transistorfet/computie/docs/posts/images/2021-09-Z80-breadboard-with-memory.jpg

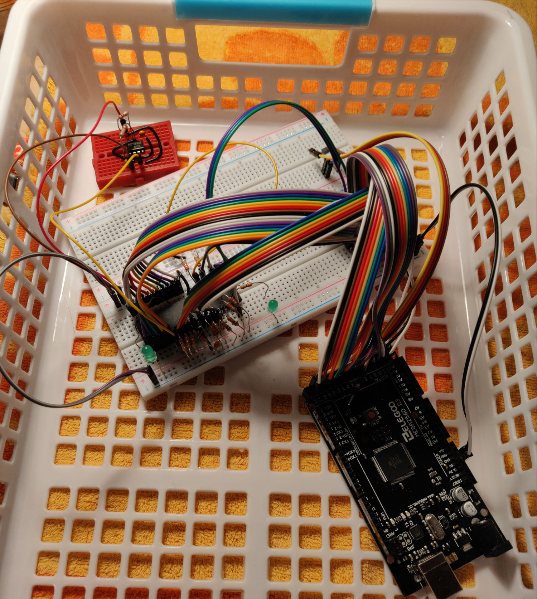
docs/posts/images/2021-09-Z80-breadboard-with-memory.jpg
