transistorfet/computie/docs/posts/images/2021-09-Z80-full-system.jpg

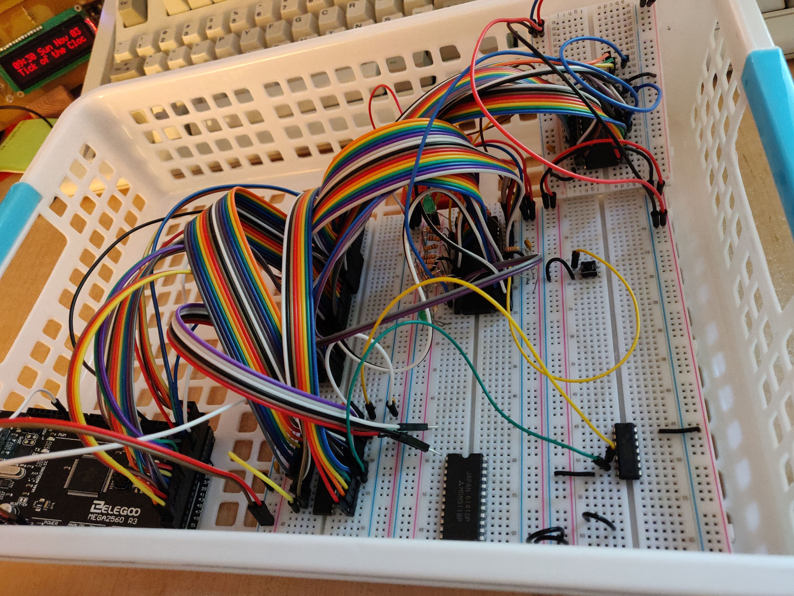
docs/posts/images/2021-09-Z80-full-system.jpg
