transistorfet/computie/images/68k-SBC-rev2/SBC-full.jpg

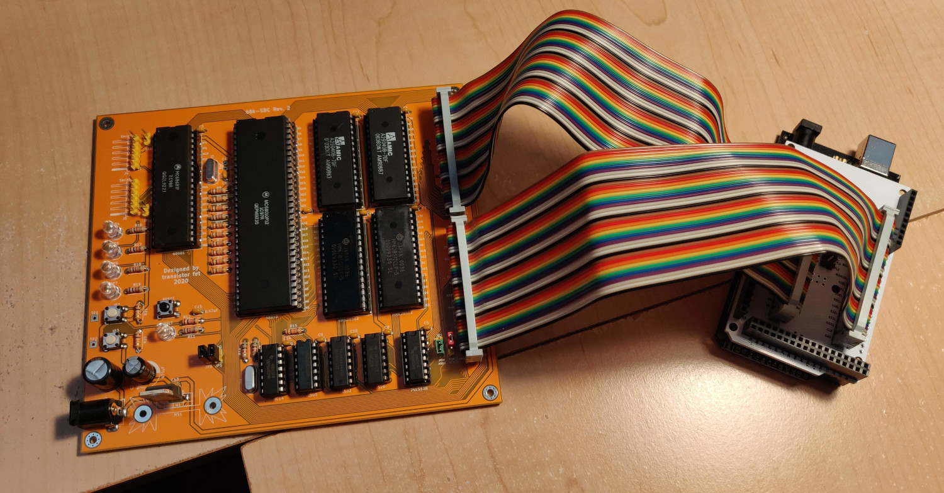
images/68k-SBC-rev2/SBC-full.jpg
