transistorfet/computie/images/68k-SMT-rev1/PCB-bottom.jpg

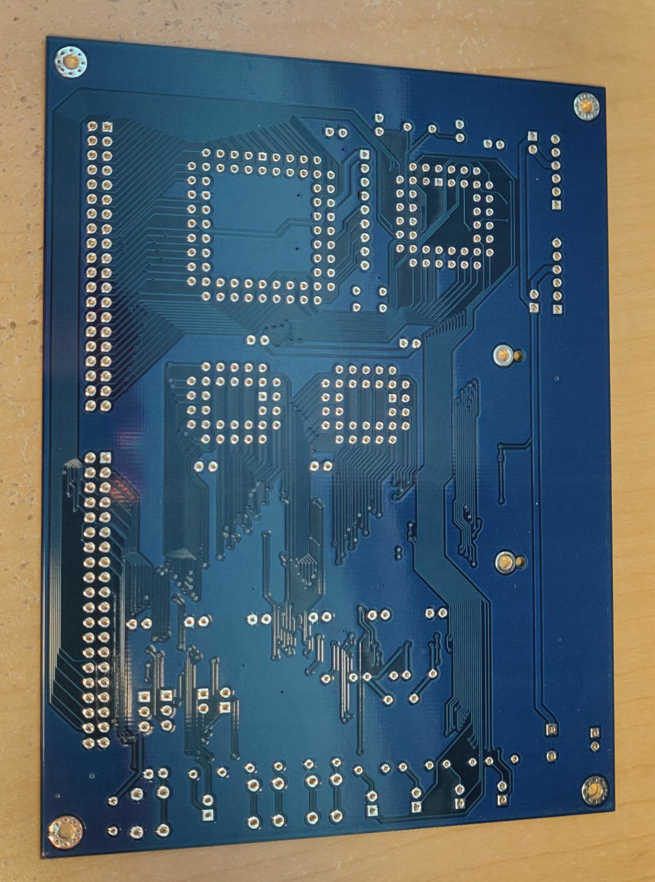
images/68k-SMT-rev1/PCB-bottom.jpg
