transistorfet/computie/images/k30-SBC-rev2/pcb-bottom.jpg

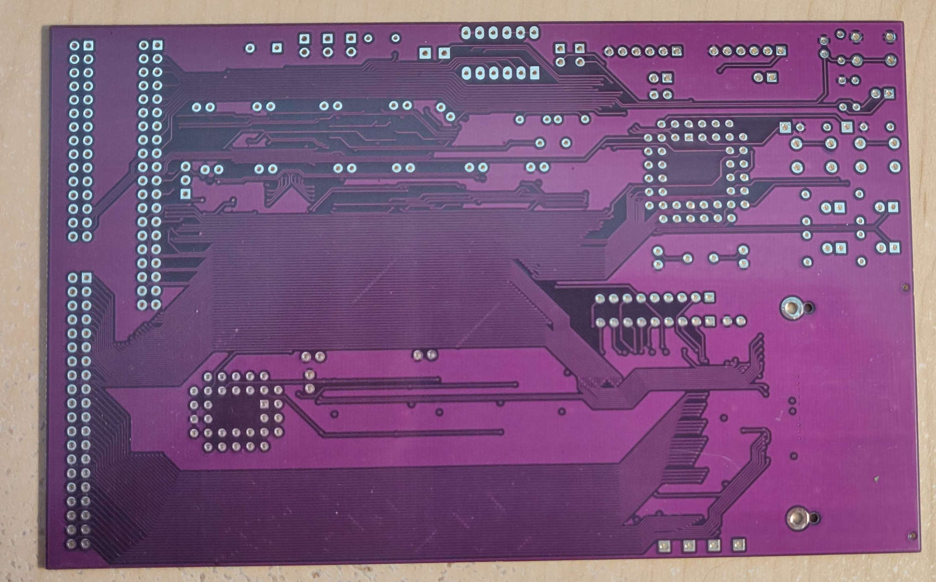
images/k30-SBC-rev2/pcb-bottom.jpg
