transistorfet/computie/hardware/Z80-NQC/Z80Supervisor/Z80Supervisor.ino

#define SERIAL_SPEED	115200

#define MEM_HADDR	0x80
#define MEM_SIZE	8192

//#define MEM_HADDR	0x08
//#define MEM_SIZE	2048
//#define MEM_WR		41 // PG0
//#define MEM_RD		40 // PG1
//#define MEM_ALE		39 // PG2

#define Z80_HADDR_PORT	PORTC
#define Z80_HADDR_PIN	PINC
#define Z80_HADDR_DDR	DDRC

#define Z80_LADDR_PORT	PORTL
#define Z80_LADDR_PIN	PINL
#define Z80_LADDR_DDR	DDRL

#define Z80_LDATA_PORT	PORTA
#define Z80_LDATA_PIN	PINA
#define Z80_LDATA_DDR	DDRA

#define Z80_BUSREQ	41 // PG0
#define Z80_BUSACK	40 // PG1
#define Z80_RESET	39 // PG2

#define Z80_MREQ	53 // PB0
#define Z80_RD		52 // PB1
#define Z80_WR		51 // PB2
#define Z80_WAIT	50 // PB3

#define Z80_IOREQ	10 // PB4
//#define Z80_IOREQ	A15 // ??

#define Z80_IS_MREQ()	(!(PINB & 0x01))
#define Z80_IS_RD()	(!(PINB & 0x02))
#define Z80_IS_WR()	(!(PINB & 0x04))
#define Z80_IS_IOREQ()	(!(PINB & 0x10))

#define Z80_SET_WAIT()	((PINB | 0x08))
#define Z80_CLR_WAIT()	((PINB & 0xF7))



#undef INLINE_NOP
#define INLINE_NOP		__asm__("nop\n\t");

#define BUS_DEVICE	0
#define BUS_CONTROLLER	1

byte bus_mode = BUS_DEVICE;

#define TTY_COMMAND	0
#define TTY_PASS	1

byte tty_mode = TTY_COMMAND;


void take_bus()
{
	digitalWrite(Z80_BUSREQ, 0);
	while (digitalRead(Z80_BUSACK)) { }
}

void release_bus()
{
	digitalWrite(Z80_BUSREQ, 1);
}

void set_bus_mode_controller()
{
	pciDisable(Z80_MREQ);
	pciDisable(Z80_IOREQ);

	take_bus();

	// Controls
	pinMode(Z80_IOREQ, OUTPUT);
	pinMode(Z80_MREQ, OUTPUT);
	pinMode(Z80_RD, OUTPUT);
	pinMode(Z80_WR, OUTPUT);
	pinMode(Z80_WAIT, INPUT);
	digitalWrite(Z80_IOREQ, 1);
	digitalWrite(Z80_MREQ, 1);
	digitalWrite(Z80_RD, 1);
	digitalWrite(Z80_WR, 1);

	// Address Bus
	Z80_HADDR_PORT = 0x00;	// A8 - A15 (for bit banged)
	Z80_HADDR_DDR = 0xFF;
	Z80_LADDR_PORT = 0x00;	// A0 - A7 (for bit banged)
	Z80_LADDR_DDR = 0xFF;

	// Data Bus
	Z80_LDATA_PORT = 0x00;	// D0 - D7
	Z80_LDATA_DDR = 0x00;

	tty_mode = TTY_COMMAND;
	bus_mode = BUS_CONTROLLER;
}

void set_bus_mode_device()
{
	// Controls
	pinMode(Z80_IOREQ, INPUT);
	pinMode(Z80_MREQ, INPUT);
	pinMode(Z80_RD, INPUT);
	pinMode(Z80_WR, INPUT);

	pinMode(Z80_WAIT, OUTPUT);
	Z80_SET_WAIT();

	pinMode(Z80_RESET, OUTPUT);
	digitalWrite(Z80_RESET, 1);

	// Address Bus
	Z80_HADDR_PORT = 0x00;	// A8 - A15 (for bit banged)
	Z80_HADDR_DDR = 0x00;
	Z80_LADDR_PORT = 0x00;	// A0 - A7 (for bit banged)
	Z80_LADDR_DDR = 0x00;

	// Data Bus
	Z80_LDATA_PORT = 0x00;	// D0 - D7
	Z80_LDATA_DDR = 0x00;

	pciSetup(Z80_MREQ);
	pciSetup(Z80_IOREQ);
	bus_mode = BUS_DEVICE;
}

/******************************
 * Serial Communications Code *
 ******************************/

#define SERIAL_SIZE	64

char serial_read_tail = 0;
char serial_read_head = 0;
char serial_avail = 0;
char serial_rb[SERIAL_SIZE];
char serial_write_head = 0;
char serial_write_tail = 0;
char serial_wb[SERIAL_SIZE];

byte read_serial()
{
	register char b;

	b = Serial.read();
	if (b == -1)
		return 0;

	if (tty_mode == TTY_PASS) {
		if (b == '`') {
			cpu_stop();
			set_bus_mode_controller();
			clear_read_buffer();
			return 0;
		}

		noInterrupts();
		//if (serial_read_head == serial_read_tail) {
		//	serial_read_head = 0;
		//	serial_read_tail = 0;	
		//}

		serial_rb[serial_read_tail++] = b;
		if (serial_read_tail >= SERIAL_SIZE)
			serial_read_tail = 0;
		interrupts();
		Serial.write(serial_get_byte());
		return 0;
	}
	else if (tty_mode == TTY_COMMAND) {
		noInterrupts();
		serial_rb[serial_read_tail] = b;
		if (b == '\n' || b == '\r') {
			serial_rb[serial_read_tail] = '\0';
			serial_avail = 1;
		}
		if (serial_read_tail < SERIAL_SIZE)
			serial_read_tail++;
		interrupts();
		return serial_avail;
	}
}

inline byte serial_get_byte()
{
	register byte value;

	noInterrupts();
	if (serial_read_head == serial_read_tail) {
		//clear_read_buffer();
		value = -1;
	} else {
		value = serial_rb[serial_read_head++];
		if (serial_read_head >= SERIAL_SIZE)
			serial_read_head = 0;
	}
	interrupts();
	return value;
}

inline byte serial_add_byte(byte data)
{
	noInterrupts();
	serial_wb[serial_write_tail++] = data;
	interrupts();
}

void clear_read_buffer()
{
	noInterrupts();
	serial_avail = 0;
	serial_read_head = 0;
	serial_read_tail = 0;
	interrupts();
}

void flush_write_buffer()
{
	if (serial_write_tail > 0) {
		byte is_running = digitalRead(Z80_BUSREQ);
		take_bus();
		noInterrupts();
		for (byte i = 0; i < serial_write_tail; i++) {
			Serial.write(serial_wb[i]);
		}
		serial_write_head = 0;
		serial_write_tail = 0;
		interrupts();
		if (is_running)
			release_bus();
	}
}



//word send_size = 128;
word send_size = 768;
byte send_mem[] = {
/*
0x00, 0x00, 0x00, 0x00, 0x00, 0x00, 0x00, 0x00, 0x00, 0x00, 0x00, 0x00, 0x00, 0x00, 0x00, 0x00, 0x00, 0x00, 0x00, 0x00, 0x00, 0x00, 0x00, 0x00, 0x00, 0x00, 0x00, 0x00, 0x00, 0x00, 0x00, 0x00,
0x3e, 0x01, 0x32, 0xff, 0x08, 0x06, 0x15, 0x11, 0x32, 0x00, 0x1a, 0x32, 0xfe, 0x08, 0x13, 0x10, 0xf9, 0x76, 0x57, 0x65, 0x6c, 0x63, 0x6f, 0x6d, 0x65, 0x20, 0x54, 0x6f, 0x20, 0x42, 0x72, 0x65,
0x61, 0x64, 0x38, 0x30, 0x24, 0x0a, 0x0a, 0x00, 0x00, 0x00, 0x00, 0x00, 0x00, 0x00, 0x00, 0x00, 0x00, 0x00, 0x00, 0x00, 0x00, 0x00, 0x00, 0x00, 0x00, 0x00, 0x00, 0x00, 0x00, 0x00, 0x00, 0x00,
0x00, 0x00, 0x00, 0x00, 0x00, 0x00, 0x00, 0x00, 0x00, 0x00, 0x00, 0x00, 0x00, 0x00, 0x00, 0x00, 0x00, 0x00, 0x00, 0x00, 0x00, 0x00, 0x00, 0x00, 0x00, 0x00, 0x00, 0x00, 0x00, 0x00, 0x00, 0x00,
*/
};


word mem_size = 4096;
byte mem[4096] = {

// C Image: 2162
//0xc3, 0x80, 0x00, 0x00, 0x00, 0x00, 0x00, 0x00, 0x00, 0x00, 0x00, 0x00, 0x00, 0x00, 0x00, 0x00, 0x00, 0x00, 0x00, 0x00, 0x00, 0x00, 0x00, 0x00, 0x00, 0x00, 0x00, 0x00, 0x00, 0x00, 0x00, 0x00, 0x00, 0x00, 0x00, 0x00, 0x00, 0x00, 0x00, 0x00, 0x00, 0x00, 0x00, 0x00, 0x00, 0x00, 0x00, 0x00, 0x00, 0x00, 0x00, 0x00, 0x00, 0x00, 0x00, 0x00, 0x00, 0x00, 0x00, 0x00, 0x00, 0x00, 0x00, 0x00, 0x00, 0x00, 0x00, 0x00, 0x00, 0x00, 0x00, 0x00, 0x00, 0x00, 0x00, 0x00, 0x00, 0x00, 0x00, 0x00, 0x00, 0x00, 0x00, 0x00, 0x00, 0x00, 0x00, 0x00, 0x00, 0x00, 0x00, 0x00, 0x00, 0x00, 0x00, 0x00, 0x00, 0x00, 0x00, 0x00, 0x00, 0x00, 0x00, 0x00, 0x00, 0x00, 0x00, 0x00, 0x00, 0x00, 0x00, 0x00, 0x00, 0x00, 0x00, 0x00, 0x00, 0x00, 0x00, 0x00, 0x00, 0x00, 0x00, 0x00, 0x00, 0x00, 0x00, 0x00, 0x31, 0x00, 0x90, 0x00, 0x00, 0x00, 0xcd, 0x00, 0x08, 0x76, 0x00, 0x00, 0x00, 0x00, 0x00, 0x00, 0x00, 0x00, 0x00, 0x00, 0x00, 0x00, 0x00, 0x00, 0x00, 0x00, 0x00, 0x00, 0x00, 0x00, 0x00, 0x00, 0x00, 0x00, 0x00, 0x00, 0x00, 0x00, 0x00, 0x00, 0x00, 0x00, 0x00, 0x00, 0x00, 0x00, 0x00, 0x00, 0x00, 0x00, 0x00, 0x00, 0x00, 0x00, 0x00, 0x00, 0x00, 0x00, 0x00, 0x00, 0x00, 0x00, 0x00, 0x00, 0x00, 0x00, 0x00, 0x00, 0x00, 0x00, 0x00, 0x00, 0x00, 0x00, 0x00, 0x00, 0x00, 0x00, 0x00, 0x00, 0x00, 0x00, 0x00, 0x00, 0x00, 0x00, 0x00, 0x00, 0x00, 0x00, 0x00, 0x00, 0x00, 0x00, 0x00, 0x00, 0x00, 0x00, 0x00, 0x00, 0x00, 0x00, 0x00, 0x00, 0x00, 0x00, 0x00, 0x00, 0x00, 0x00, 0x00, 0x00, 0x00, 0x00, 0x00, 0x00, 0x00, 0x00, 0x00, 0x00, 0x00, 0x00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
, 0x00, 0x00, 0x00, 0x00, 0x00, 0x00, 0x00, 0x00, 0x00, 0x00, 0x00, 0x00, 0x00, 0x00, 0x00, 0x00, 0x00, 0x00, 0x00, 0x00, 0x00, 0x00, 0x00, 0x00, 0x00, 0x00, 0x00, 0x00, 0x00, 0x00, 0x00, 0x00, 0x00, 0x00, 0x00, 0x00, 0x00, 0x00, 0x00, 0x00, 0x00, 0x00, 0x00, 0x00, 0x00, 0x00, 0x00, 0x00, 0xdd, 0xe5, 0xdd, 0x21, 0x00, 0x00, 0xdd, 0x39, 0x0e, 0x00, 0xdd, 0x6e, 0x04, 0xdd, 0x66, 0x05, 0x06, 0x00, 0x09, 0x7e, 0xb7, 0x28, 0x14, 0xed, 0x5b, 0x56, 0x08, 0x79, 0x0c, 0xdd, 0x86, 0x04, 0x6f, 0x3e, 0x00, 0xdd, 0x8e, 0x05, 0x67, 0x7e, 0x12, 0x18, 0xdf, 0xdd, 0xe1, 0xc9, 0x2a, 0x58, 0x08, 0x36, 0x01, 0x2a, 0x5a, 0x08, 0xe5, 0xcd, 0x00, 0x08, 0xf1, 0x21, 0x00, 0x00, 0xc9, 0x57, 0x65, 0x6c, 0x63, 0x6f, 0x6d, 0x65, 0x20, 0x74, 0x6f, 0x20, 0x74, 0x68, 0x65, 0x20, 0x74, 0x68, 0x69, 0x6e, 0x67, 0x21, 0x0a, 0x00, 0x00, 0x00, 0x00, 0x00, 0x00, 0x00, 0x01, 0x06, 0x00, 0x78, 0xb1, 0x28, 0x08, 0x11, 0x56, 0x08, 0x21, 0x6c, 0x08, 0xed, 0xb0, 0xc9, 0xfe, 0x00, 0xff, 0x00, 0x3f, 0x08

// C Image: 2165
//0xc3, 0x80, 0x00, 0x00, 0x00, 0x00, 0x00, 0x00, 0x00, 0x00, 0x00, 0x00, 0x00, 0x00, 0x00, 0x00, 0x00, 0x00, 0x00, 0x00, 0x00, 0x00, 0x00, 0x00, 0x00, 0x00, 0x00, 0x00, 0x00, 0x00, 0x00, 0x00, 0x00, 0x00, 0x00, 0x00, 0x00, 0x00, 0x00, 0x00, 0x00, 0x00, 0x00, 0x00, 0x00, 0x00, 0x00, 0x00, 0x00, 0x00, 0x00, 0x00, 0x00, 0x00, 0x00, 0x00, 0x00, 0x00, 0x00, 0x00, 0x00, 0x00, 0x00, 0x00, 0x00, 0x00, 0x00, 0x00, 0x00, 0x00, 0x00, 0x00, 0x00, 0x00, 0x00, 0x00, 0x00, 0x00, 0x00, 0x00, 0x00, 0x00, 0x00, 0x00, 0x00, 0x00, 0x00, 0x00, 0x00, 0x00, 0x00, 0x00, 0x00, 0x00, 0x00, 0x00, 0x00, 0x00, 0x00, 0x00, 0x00, 0x00, 0x00, 0x00, 0x00, 0x00, 0x00, 0x00, 0x00, 0x00, 0x00, 0x00, 0x00, 0x00, 0x00, 0x00, 0x00, 0x00, 0x00, 0x00, 0x00, 0x00, 0x00, 0x00, 0x00, 0x00, 0x00, 0x00, 0x31, 0x00, 0x80, 0xcd, 0x5c, 0x08, 0xcd, 0x2e, 0x08, 0x76, 0x00, 0x00, 0x00, 0x00, 0x00, 0x00, 0x00, 0x00, 0x00, 0x00, 0x00, 0x00, 0x00, 0x00, 0x00, 0x00, 0x00, 0x00, 0x00, 0x00, 0x00, 0x00, 0x00, 0x00, 0x00, 0x00, 0x00, 0x00, 0x00, 0x00, 0x00, 0x00, 0x00, 0x00, 0x00, 0x00, 0x00, 0x00, 0x00, 0x00, 0x00, 0x00, 0x00, 0x00, 0x00, 0x00, 0x00, 0x00, 0x00, 0x00, 0x00, 0x00, 0x00, 0x00, 0x00, 0x00, 0x00, 0x00, 0x00, 0x00, 0x00, 0x00, 0x00, 0x00, 0x00, 0x00, 0x00, 0x00, 0x00, 0x00, 0x00, 0x00, 0x00, 0x00, 0x00, 0x00, 0x00, 0x00, 0x00, 0x00, 0x00, 0x00, 0x00, 0x00, 0x00, 0x00, 0x00, 0x00, 0x00, 0x00, 0x00, 0x00, 0x00, 0x00, 0x00, 0x00, 0x00, 0x00, 0x00, 0x00, 0x00, 0x00, 0x00, 0x00, 0x00, 0x00, 0x00, 0x00, 0x00, 0x00, 0x00, 0x00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

//// Welcome - Test Stack: 512
//0xc3, 0x80, 0x00, 0x00, 0x00, 0x00, 0x00, 0x00, 0x00, 0x00, 0x00, 0x00, 0x00, 0x00, 0x00, 0x00, 0x00, 0x00, 0x00, 0x00, 0x00, 0x00, 0x00, 0x00, 0x00, 0x00, 0x00, 0x00, 0x00, 0x00, 0x00, 0x00, 0x00, 0x00, 0x00, 0x00, 0x00, 0x00, 0x00, 0x00, 0x00, 0x00, 0x00, 0x00, 0x00, 0x00, 0x00, 0x00, 0x00, 0x00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

//// Welcome - Test Stack, No External Ram: 512
//0xc3, 0x80, 0x00, 0x00, 0x00, 0x00, 0x00, 0x00, 0x00, 0x00, 0x00, 0x00, 0x00, 0x00, 0x00, 0x00, 0x00, 0x00, 0x00, 0x00, 0x00, 0x00, 0x00, 0x00, 0x00, 0x00, 0x00, 0x00, 0x00, 0x00, 0x00, 0x00, 0x00, 0x00, 0x00, 0x00, 0x00, 0x00, 0x00, 0x00, 0x00, 0x00, 0x00, 0x00, 0x00, 0x00, 0x00, 0x00, 0x00, 0x00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



//// MemTest: 512
// ADDR: 2000h
//0xc3, 0x80, 0x00, 0x00, 0x00, 0x00, 0x00, 0x00, 0x00, 0x00, 0x00, 0x00, 0x00, 0x00, 0x00, 0x00, 0x00, 0x00, 0x00, 0x00, 0x00, 0x00, 0x00, 0x00, 0x00, 0x00, 0x00, 0x00, 0x00, 0x00, 0x00, 0x00, 0x00, 0x00, 0x00, 0x00, 0x00, 0x00, 0x00, 0x00, 0x00, 0x00, 0x00, 0x00, 0x00, 0x00, 0x00, 0x00, 0x00, 0x00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
// ADDR: 8000h
//0xc3, 0x80, 0x00, 0x00, 0x00, 0x00, 0x00, 0x00, 0x00, 0x00, 0x00, 0x00, 0x00, 0x00, 0x00, 0x00, 0x00, 0x00, 0x00, 0x00, 0x00, 0x00, 0x00, 0x00, 0x00, 0x00, 0x00, 0x00, 0x00, 0x00, 0x00, 0x00, 0x00, 0x00, 0x00, 0x00, 0x00, 0x00, 0x00, 0x00, 0x00, 0x00, 0x00, 0x00, 0x00, 0x00, 0x00, 0x00, 0x00, 0x00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

//0x00, 0xc3, 0x80, 0x00, 0x00, 0x00, 0x00, 0x00, 0xed, 0x4d, 0x00, 0x00, 0x00, 0x00, 0x00, 0x00, 0xed, 0x4d, 0x00, 0x00, 0x00, 0x00, 0x00, 0x00, 0xed, 0x4d, 0x00, 0x00, 0x00, 0x00, 0x00, 0x00, 0xed, 0x4d, 0x00, 0x00, 0x00, 0x00, 0x00, 0x00, 0xed, 0x4d, 0x00, 0x00, 0x00, 0x00, 0x00, 0x00, 0xed, 0x4d, 0x00, 0x00, 0x00, 0x00, 0x00, 0x00, 0x00, 0x00, 0x00, 0x00, 0x00, 0x00, 0x00, 0x00, 0x00, 0x00, 0x00, 0x00, 0x00, 0x00, 0x00, 0x00, 0x00, 0x00, 0x00, 0x00, 0x00, 0x00, 0x00, 0x00, 0x00, 0x00, 0x00, 0x00, 0x00, 0x00, 0x00, 0x00, 0x00, 0x00, 0x00, 0x00, 0x00, 0x00, 0x00, 0x00, 0x00, 0x00, 0x00, 0x00, 0x00, 0x00, 0x00, 0x00, 0x00, 0x00, 0x00, 0x00, 0x00, 0x00, 0x00, 0x00, 0x00, 0x00, 0x00, 0x00, 0x00, 0x00, 0x00, 0x00, 0x00, 0x00, 0x00, 0x00, 0x00, 0x00, 0x00, 0x00, 0x31, 0x00, 0x0c, 0xcd, 0x02, 0x08, 0xcd, 0x22, 0x01, 0x76, 0x00, 0x00, 0x00, 0x00, 0x00, 0x00, 0x00, 0x00, 0x00, 0x00, 0x00, 0x00, 0x00, 0x00, 0x00, 0x00, 0x00, 0x00, 0x00, 0x00, 0x00, 0x00, 0x00, 0x00, 0x00, 0x00, 0x00, 0x00, 0x00, 0x00, 0x00, 0x00, 0x00, 0x00, 0x00, 0x00, 0x00, 0x00, 0x00, 0x00, 0x00, 0x00, 0x00, 0x00, 0x00, 0x00, 0x00, 0x00, 0x00, 0x00, 0x00, 0x00, 0x00, 0x00, 0x00, 0x00, 0x00, 0x00, 0x00, 0x00, 0x00, 0x00, 0x00, 0x00, 0x00, 0x00, 0x00, 0x00, 0x00, 0x00, 0x00, 0x00, 0x00, 0x00, 0x00, 0x00, 0x00, 0x00, 0x00, 0x00, 0x00, 0x00, 0x00, 0x00, 0x00, 0x00, 0x00, 0x00, 0x00, 0x00, 0x00, 0x00, 0x00, 0x00, 0x00, 0x00, 0x00, 0x00, 0x00, 0x00, 0x00, 0x00, 0x00, 0x00, 0x00, 0x00, 0x00, 0x00, 0x00, 0x00, 0x00, 0x00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
, 0x00, 0x00, 0x00, 0x00, 0x00, 0x00, 0x00, 0x00, 0x00, 0x00, 0x00, 0x00, 0x00, 0x00, 0x00, 0x00, 0x00, 0x00, 0x00, 0x00, 0x00, 0x00, 0x00, 0x00, 0x00, 0x00, 0x00, 0x00, 0x00, 0x00, 0x00, 0x00, 0x00, 0x00, 0x00, 0x00, 0x00, 0x00, 0x00, 0x00, 0x00, 0x00, 0x00, 0x00, 0x00, 0x00, 0x00, 0x00, 0x00, 0x00, 0x01, 0x02, 0x00, 0x78, 0xb1, 0x28, 0x08, 0x11, 0x00, 0x08, 0x21, 0x12, 0x08, 0xed, 0xb0, 0xc9, 0x32, 0x01, 
//0x00, 0xc3, 0x80, 0x00, 0x00, 0x00, 0x00, 0x00, 0xed, 0x4d, 0x00, 0x00, 0x00, 0x00, 0x00, 0x00, 0xed, 0x4d, 0x00, 0x00, 0x00, 0x00, 0x00, 0x00, 0xed, 0x4d, 0x00, 0x00, 0x00, 0x00, 0x00, 0x00, 0xed, 0x4d, 0x00, 0x00, 0x00, 0x00, 0x00, 0x00, 0xed, 0x4d, 0x00, 0x00, 0x00, 0x00, 0x00, 0x00, 0xed, 0x4d, 0x00, 0x00, 0x00, 0x00, 0x00, 0x00, 0x00, 0x00, 0x00, 0x00, 0x00, 0x00, 0x00, 0x00, 0x00, 0x00, 0x00, 0x00, 0x00, 0x00, 0x00, 0x00, 0x00, 0x00, 0x00, 0x00, 0x00, 0x00, 0x00, 0x00, 0x00, 0x00, 0x00, 0x00, 0x00, 0x00, 0x00, 0x00, 0x00, 0x00, 0x00, 0x00, 0x00, 0x00, 0x00, 0x00, 0x00, 0x00, 0x00, 0x00, 0x00, 0x00, 0x00, 0x00, 0x00, 0x00, 0x00, 0x00, 0x00, 0x00, 0x00, 0x00, 0x00, 0x00, 0x00, 0x00, 0x00, 0x00, 0x00, 0x00, 0x00, 0x00, 0x00, 0x00, 0x00, 0x00, 0x00, 0x00, 0x31, 0x00, 0x0c, 0xcd, 0x02, 0x08, 0xcd, 0xc2, 0x00, 0x76, 0x00, 0x00, 0x00, 0x00, 0x00, 0x00, 0x00, 0x00, 0x00, 0x00, 0x00, 0x00, 0x00, 0x00, 0x00, 0x00, 0x00, 0x00, 0x00, 0x00, 0x00, 0x00, 0x0e, 0x00, 0x21, 0x02, 0x00, 0x39, 0x7e, 0x23, 0x66, 0x6f, 0x06, 0x00, 0x09, 0x7e, 0xb7, 0xc8, 0x79, 0x0c, 0x21, 0x02, 0x00, 0x39, 0x86, 0x5f, 0x3e, 0x00, 0x23, 0x8e, 0x57, 0x1a, 0xd3, 0xfe, 0x18, 0xe0, 0x3e, 0x01, 0xd3, 0xff, 0x2a, 0x00, 0x08, 0xe5, 0xcd, 0xa0, 0x00, 0xf1, 0x21, 0x00, 0x00, 0xc9, 0x57, 0x65, 0x6c, 0x63, 0x6f, 0x6d, 0x65, 0x20, 0x74, 0x6f, 0x20, 0x74, 0x68, 0x65, 0x20, 0x74, 0x68, 0x69, 0x6e, 0x67, 0x21, 0x0a, 0x00, 0x00, 0x00, 0x00, 0x00, 0x00, 0x00, 0x00, 0x00, 0x00, 0x00, 0x00, 0x00, 0x00, 0x00, 0x00, 0x00, 0x00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
, 0x00, 0x00, 0x00, 0x00, 0x00, 0x00, 0x00, 0x00, 0x00, 0x00, 0x00, 0x00, 0x00, 0x00, 0x00, 0x00, 0x00, 0x00, 0x00, 0x00, 0x00, 0x00, 0x00, 0x00, 0x00, 0x00, 0x00, 0x00, 0x00, 0x00, 0x00, 0x00, 0x00, 0x00, 0x00, 0x00, 0x00, 0x00, 0x00, 0x00, 0x00, 0x00, 0x00, 0x00, 0x00, 0x00, 0x00, 0x00, 0x00, 0x00, 0x01, 0x02, 0x00, 0x78, 0xb1, 0x28, 0x08, 0x11, 0x00, 0x08, 0x21, 0x12, 0x08, 0xed, 0xb0, 0xc9, 0xd2, 0x00,
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
